Matt5sean3/doorbell-pin-daemon/src/pin_set_state.c

#include "pin_daemon_internal.h"

int pin_set_state(
    const PinOutConfiguration* pin_out,
    PinState state) {
  write_to_file(
      pin_out->value_path,
      state == PIN_STATE_LOW ? "0" :
      state == PIN_STATE_HIGH ? "1" :
      "0");
}
